Student-Satellite-IITB/Electrical-Power-System/Testing/Solar_Array_Simulator_SPICE/SAS.png

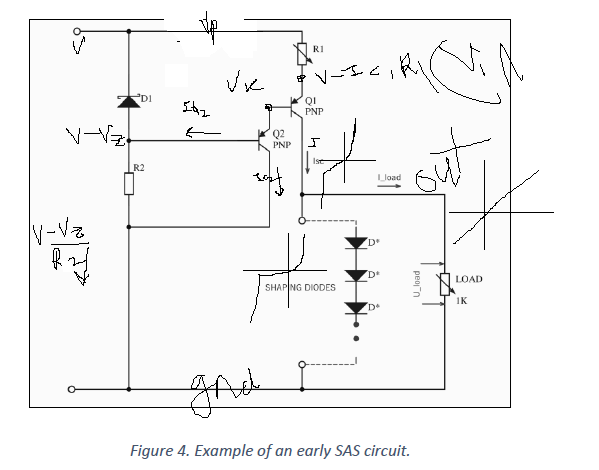
Testing/Solar_Array_Simulator_SPICE/SAS.png
