Student-Satellite-IITB/Electrical-Power-System/DevelopmentBoards/Battery/BatteryUnit/BatteryUnit.kicad_sch

## KiCad design DevelopmentBoards/Battery/BatteryUnit/BatteryUnit.kicad_sch (2024-07-16)

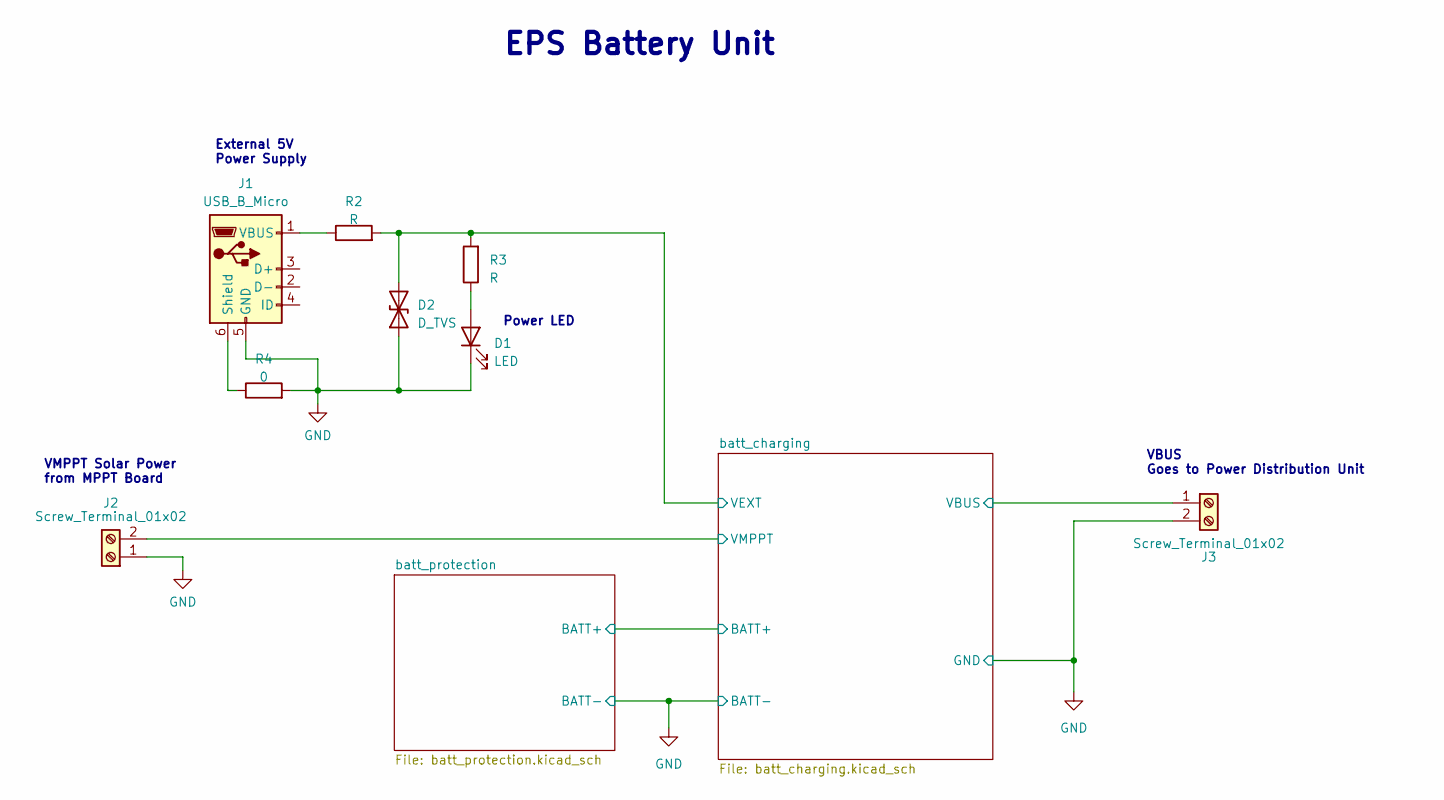
[picture p43: schematic BatteryUnit.kicad_sch]

Parts:
D1: LED
D2: D_TVS
J1: USB_B_Micro
J2, J3: Screw_Terminal_01x02
R2, R3: R
R4: 0

Connections:
GND: D1.1 (K), D2.1 (A1), J1.5 (GND), J2.1, J3.2, R4.2
unnamed: D1.2 (A), R3.1
unnamed: J1.1 (VBUS), R2.1
unnamed: J1.6 (Shield), R4.1
VBUS: J3.1
VEXT: D2.2 (A2), R2.2, R3.2
VMPPT: J2.2

Notes on the sheet:
VMPPT Solar Power from MPPT Board
Power LED
EPS Battery Unit
VBUS Goes to Power Distribution Unit
External 5V Power Supply
