Student-Satellite-IITB/Electrical-Power-System/DevelopmentBoards/Battery/BatteryUnit/batt_charging.kicad_sch

## KiCad design DevelopmentBoards/Battery/BatteryUnit/batt_charging.kicad_sch (2024-07-18)

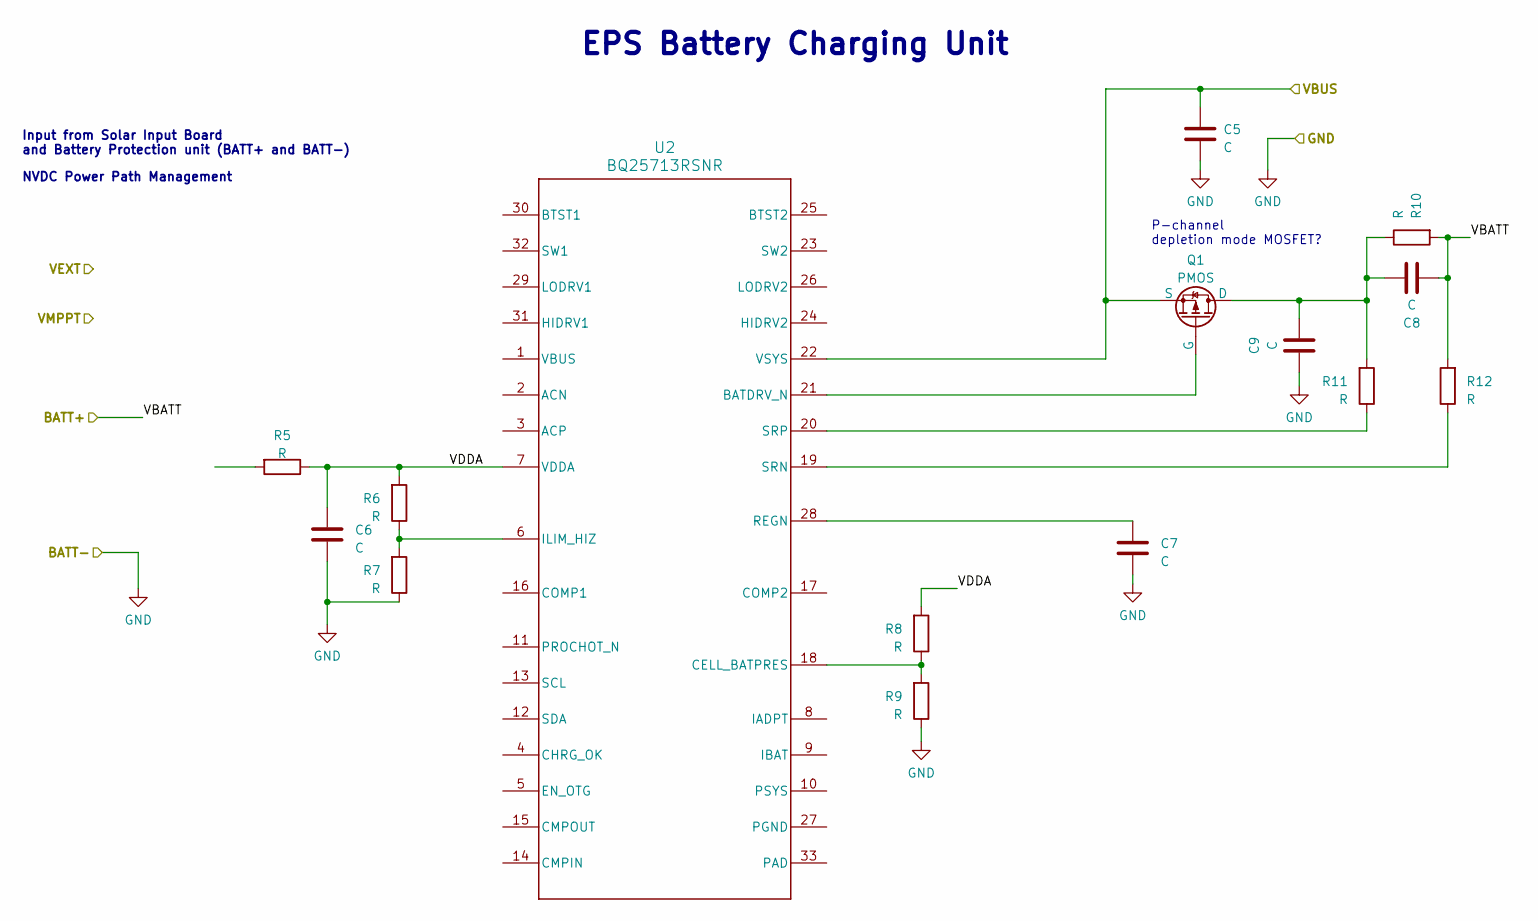
[picture p44: schematic batt_charging.kicad_sch]

Parts:
C5, C6, C7, C8, C9: C
Q1: PMOS
R5, R6, R7, R8, R9, R10, R11, R12: R
U2: BQ25713RSNR; RSN0032B

Connections:
BATT+: C8.1, R10.2, R12.2
GND: C5.2, C6.2, C7.2, C9.1, R7.1, R9.1
unnamed: C7.1, U2.28 (REGN)
unnamed: C8.2, C9.2, Q1.1 (D), R10.1, R11.2
unnamed: Q1.2 (G), U2.21 (BATDRV_N)
unnamed: R6.1, R7.2, U2.6 (ILIM_HIZ)
unnamed: R8.1, R9.2, U2.18 (CELL_BATPRES)
unnamed: R11.1, U2.20 (SRP)
unnamed: R12.1, U2.19 (SRN)
VBUS: C5.1, Q1.3 (S), U2.22 (VSYS)
VDDA: C6.1, R5.1, R6.2, R8.2, U2.7 (VDDA)

Notes on the sheet:
Input from Solar Input Board and Battery Protection unit (BATT+ and BATT-)
EPS Battery Charging Unit
P-channel depletion mode MOSFET?
NVDC Power Path Management
