Student-Satellite-IITB/Electrical-Power-System/DevelopmentBoards/Battery/BatteryUnit/batt_protection.kicad_sch

## KiCad design DevelopmentBoards/Battery/BatteryUnit/batt_protection.kicad_sch (2024-07-16)

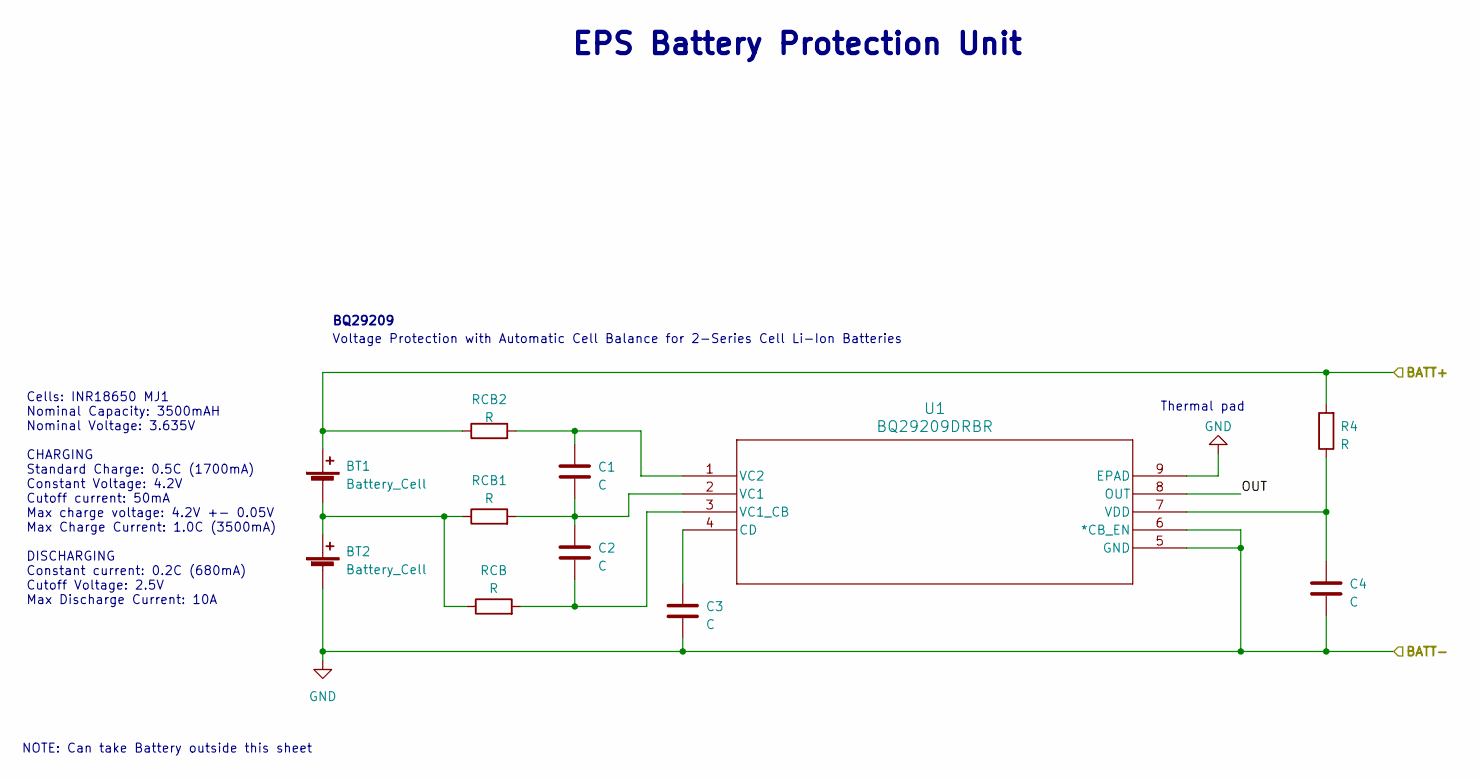
[picture p45: schematic batt_protection.kicad_sch]

Parts:
BT1, BT2: Battery_Cell
C1, C2, C3, C4: C
R4: R
RCB, RCB1, RCB2: R
U1: BQ29209DRBR; DRB8_1P6X2P4

Connections:
BATT+: BT1.1 (+), R4.2, RCB2.1
GND: BT2.2 (-), C3.2, C4.2, U1.5 (GND), U1.6 (*CB_EN), U1.9 (EPAD)
unnamed: BT1.2 (-), BT2.1 (+), RCB.1, RCB1.1
unnamed: C1.1, RCB2.2, U1.1 (VC2)
unnamed: C1.2, C2.1, RCB1.2, U1.2 (VC1)
unnamed: C2.2, RCB.2, U1.3 (VC1_CB)
unnamed: C3.1, U1.4 (CD)
unnamed: C4.1, R4.1, U1.7 (VDD)
OUT: U1.8 (OUT)

Notes on the sheet:
EPS Battery Protection Unit
Voltage Protection with Automatic Cell Balance for 2-Series Cell Li-Ion Batteries
Cells: INR18650 MJ1 Nominal Capacity: 3500mAH Nominal Voltage: 3.635V CHARGING Standard Charge: 0.5C (1700mA) Constant Voltage: 4.2V Cutoff current: 50mA Max charge voltage: 4.2V +- 0.05V Max Charge Current: 1.0C (3500mA) DISCHARGING Constant current: 0.2C (680mA) Cutoff Voltage: 2.5V Max Discharge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
BQ29209
Thermal pad
NOTE: Can take Battery outside this sheet
